piro-s/thermostat/datashits/Щелкаем реле правильно_ коммутация мощных нагрузок _ Хабр_files/0d3640cc47d04c21a2d8dd4c8c17a69a.png

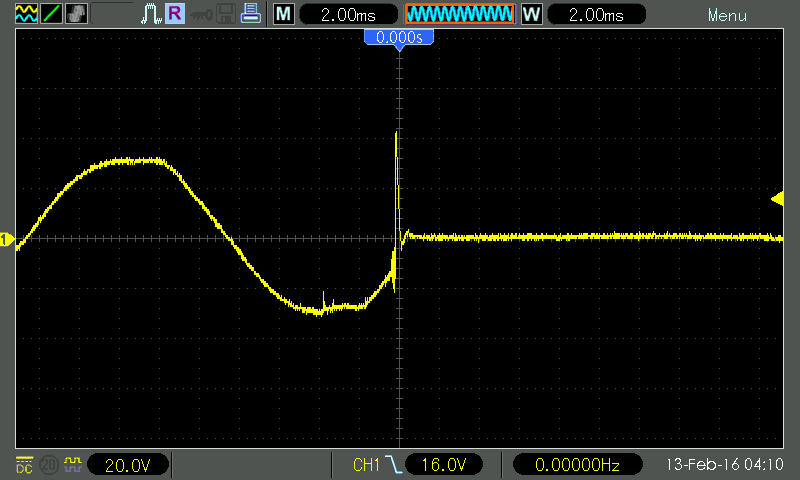
datashits/Щелкаем реле правильно_ коммутация мощных нагрузок _ Хабр_files/0d3640cc47d04c21a2d8dd4c8c17a69a.png
