piro-s/thermostat/datashits/Щелкаем реле правильно_ коммутация мощных нагрузок _ Хабр_files/2d4d09c20a6148d1adfdadfce8923db4.png

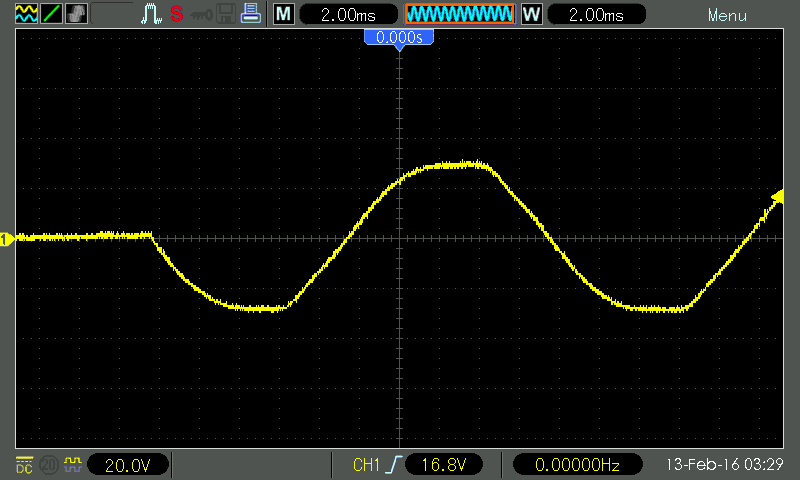
datashits/Щелкаем реле правильно_ коммутация мощных нагрузок _ Хабр_files/2d4d09c20a6148d1adfdadfce8923db4.png
