piro-s/thermostat/datashits/Щелкаем реле правильно_ коммутация мощных нагрузок _ Хабр_files/3cb6dfe0c0b29f546c39c100f3efd193.jpg

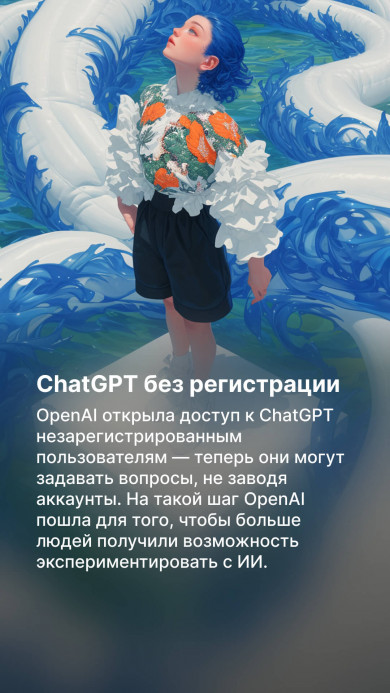
datashits/Щелкаем реле правильно_ коммутация мощных нагрузок _ Хабр_files/3cb6dfe0c0b29f546c39c100f3efd193.jpg
