piro-s/thermostat/datashits/Щелкаем реле правильно_ коммутация мощных нагрузок _ Хабр_files/3f51d74c4c32d6d4213a719e6e2add86.jpg

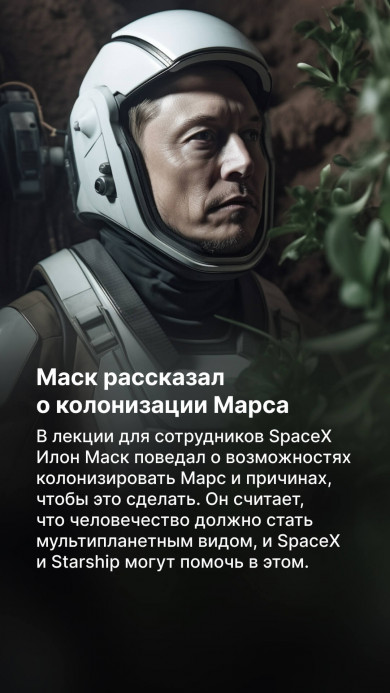
datashits/Щелкаем реле правильно_ коммутация мощных нагрузок _ Хабр_files/3f51d74c4c32d6d4213a719e6e2add86.jpg
