piro-s/thermostat/datashits/Щелкаем реле правильно_ коммутация мощных нагрузок _ Хабр_files/8a666dc12d0648c7a57a527654e74f90.png

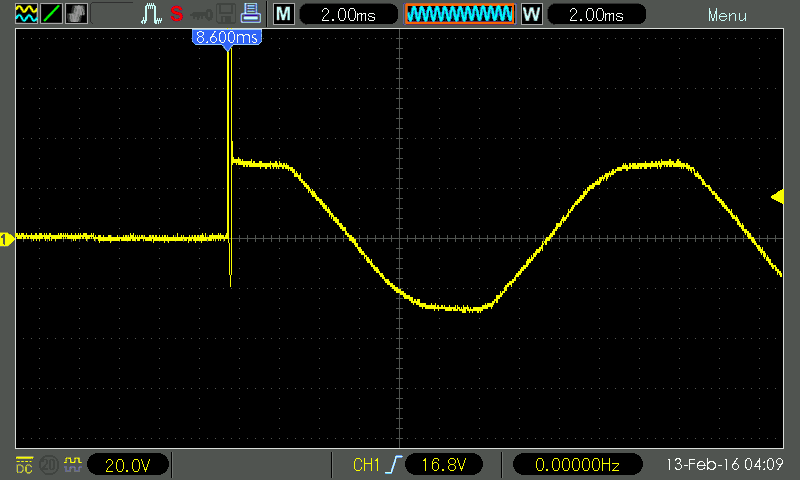
datashits/Щелкаем реле правильно_ коммутация мощных нагрузок _ Хабр_files/8a666dc12d0648c7a57a527654e74f90.png
