piro-s/thermostat/datashits/Щелкаем реле правильно_ коммутация мощных нагрузок _ Хабр_files/38e868bb6e074741b2f072006ed7f731.png

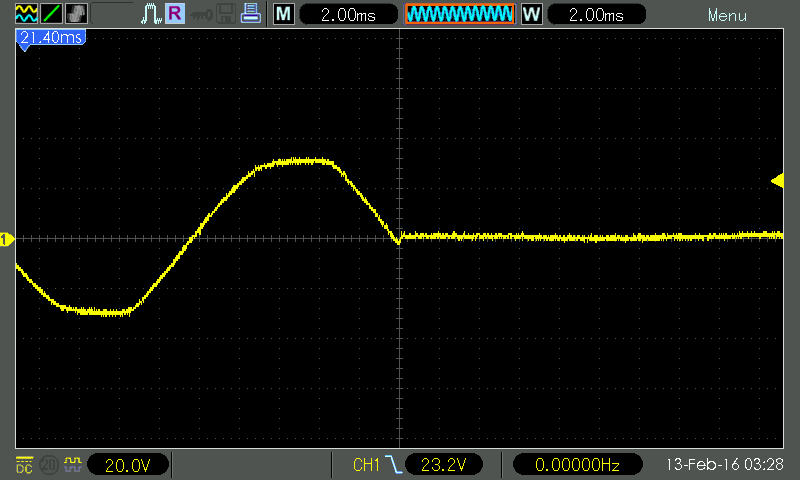
datashits/Щелкаем реле правильно_ коммутация мощных нагрузок _ Хабр_files/38e868bb6e074741b2f072006ed7f731.png
