piro-s/thermostat/datashits/Щелкаем реле правильно_ коммутация мощных нагрузок _ Хабр_files/93b239661d7f43c48de33240623da11f.png

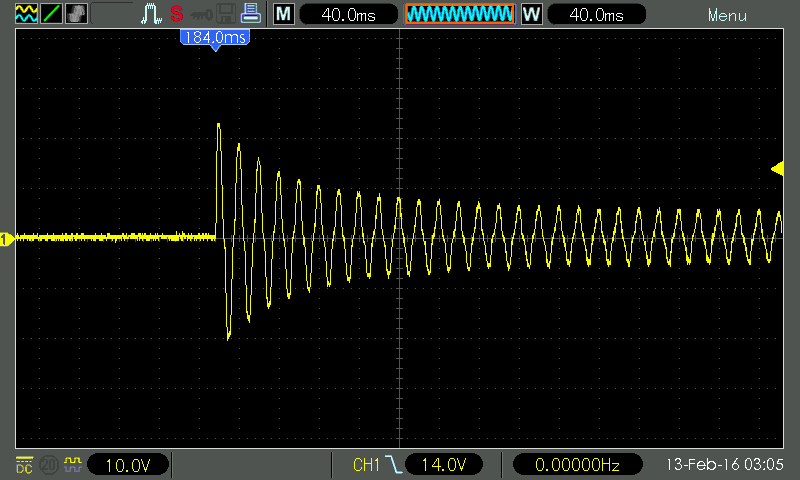
datashits/Щелкаем реле правильно_ коммутация мощных нагрузок _ Хабр_files/93b239661d7f43c48de33240623da11f.png
