piro-s/thermostat/datashits/Щелкаем реле правильно_ коммутация мощных нагрузок _ Хабр_files/03091f08f97542e8aeee063b271ce8ba.png

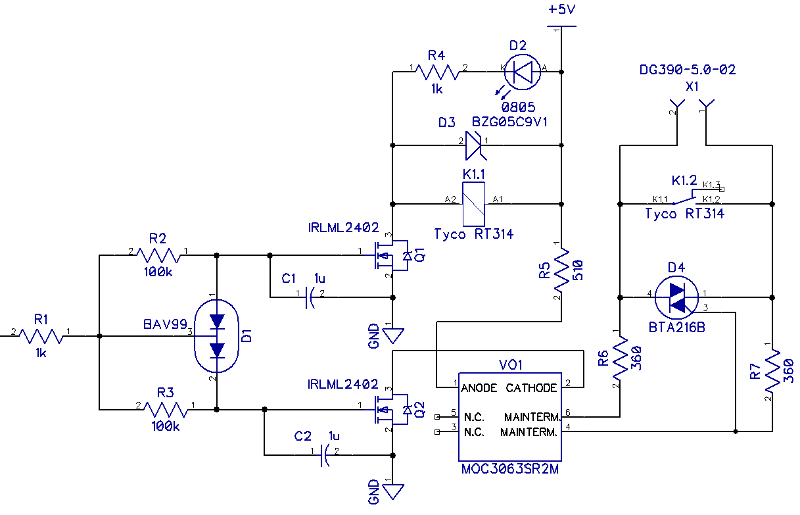
datashits/Щелкаем реле правильно_ коммутация мощных нагрузок _ Хабр_files/03091f08f97542e8aeee063b271ce8ba.png
