piro-s/thermostat/datashits/Щелкаем реле правильно_ коммутация мощных нагрузок _ Хабр_files/0437124ab8b0493c8f42604423db183e.png

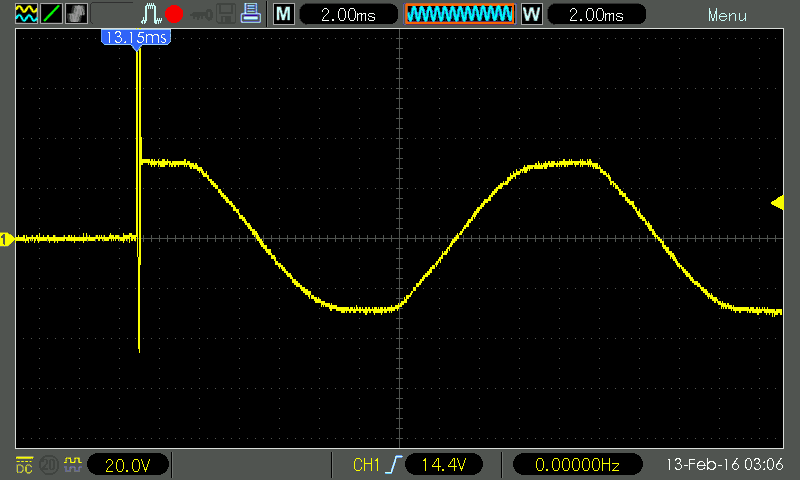
datashits/Щелкаем реле правильно_ коммутация мощных нагрузок _ Хабр_files/0437124ab8b0493c8f42604423db183e.png
