piro-s/thermostat/datashits/Щелкаем реле правильно_ коммутация мощных нагрузок _ Хабр_files/c421d6eea55148a8b3472a98f32bb692.jpg

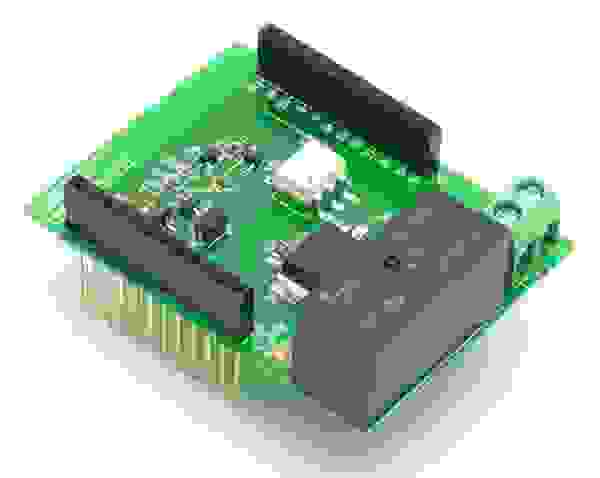
datashits/Щелкаем реле правильно_ коммутация мощных нагрузок _ Хабр_files/c421d6eea55148a8b3472a98f32bb692.jpg
